Archive-663/lomoLCA/ASSETS/PHOTO/SAMPLE/fuji (3).jpg

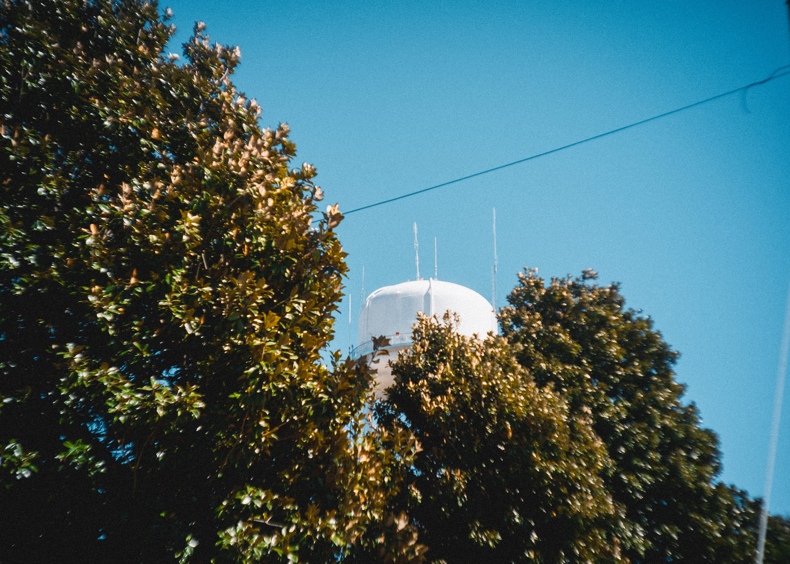
ASSETS/PHOTO/SAMPLE/fuji (3).jpg
