Archive-663/lomoLCA/ASSETS/PHOTO/SAMPLE/fuji (5).jpg

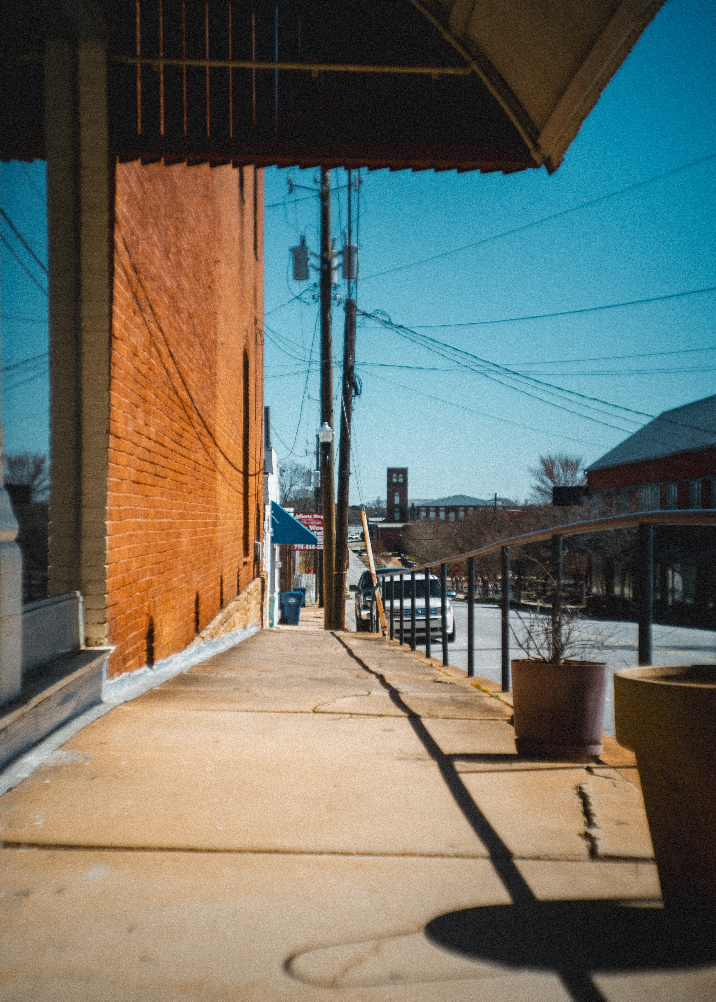
ASSETS/PHOTO/SAMPLE/fuji (5).jpg
