Archive-663/lomoLCA/ASSETS/PHOTO/SAMPLE/fuji (6).jpg

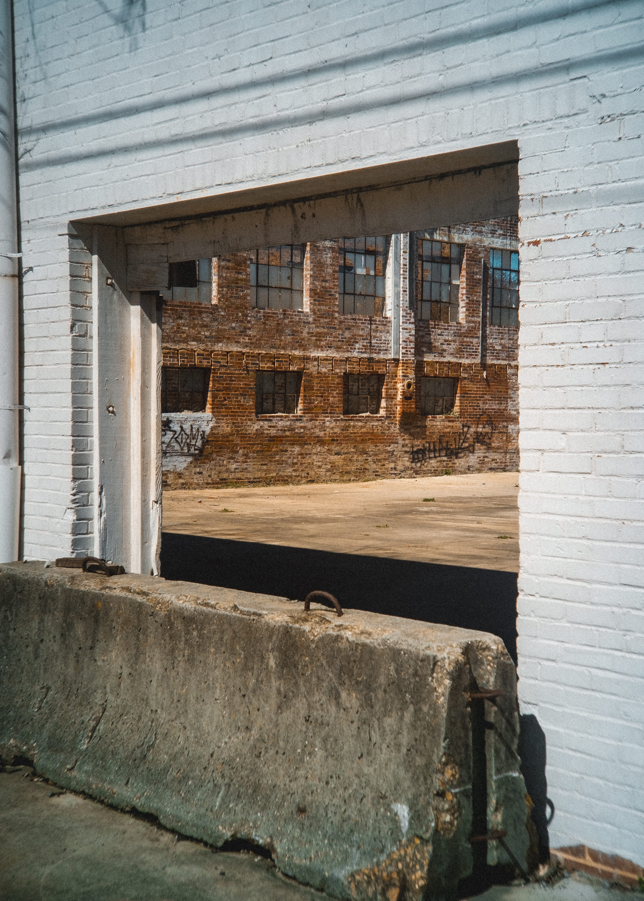
ASSETS/PHOTO/SAMPLE/fuji (6).jpg
