Archive-663/lomoLCA/ASSETS/PHOTO/SAMPLE/fuji (8).jpg

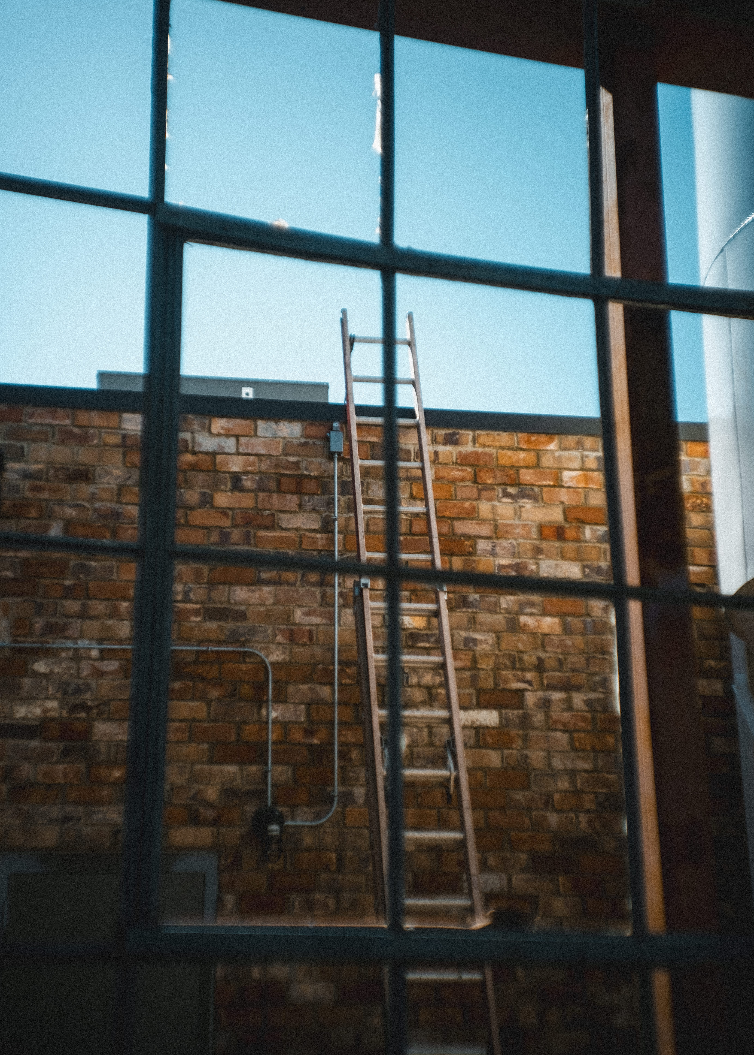
ASSETS/PHOTO/SAMPLE/fuji (8).jpg
