Archive-663/lomoLCA/ASSETS/PHOTO/SAMPLE/fuji (9).jpg

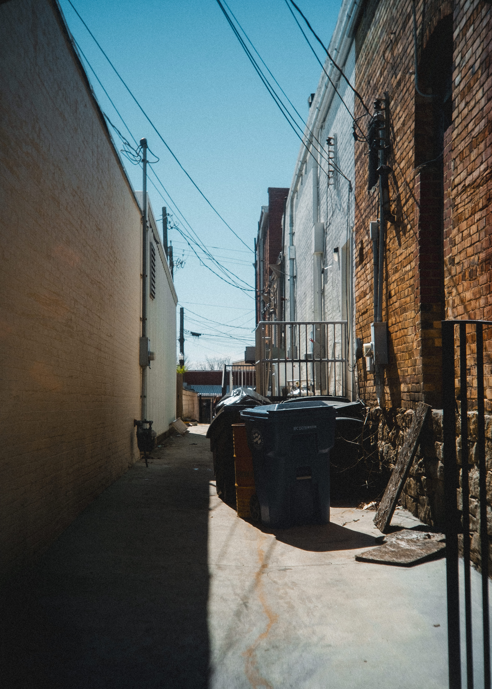
ASSETS/PHOTO/SAMPLE/fuji (9).jpg
