Archive-663/lomoLCA/ASSETS/PHOTO/SAMPLE/fuji (12).jpg

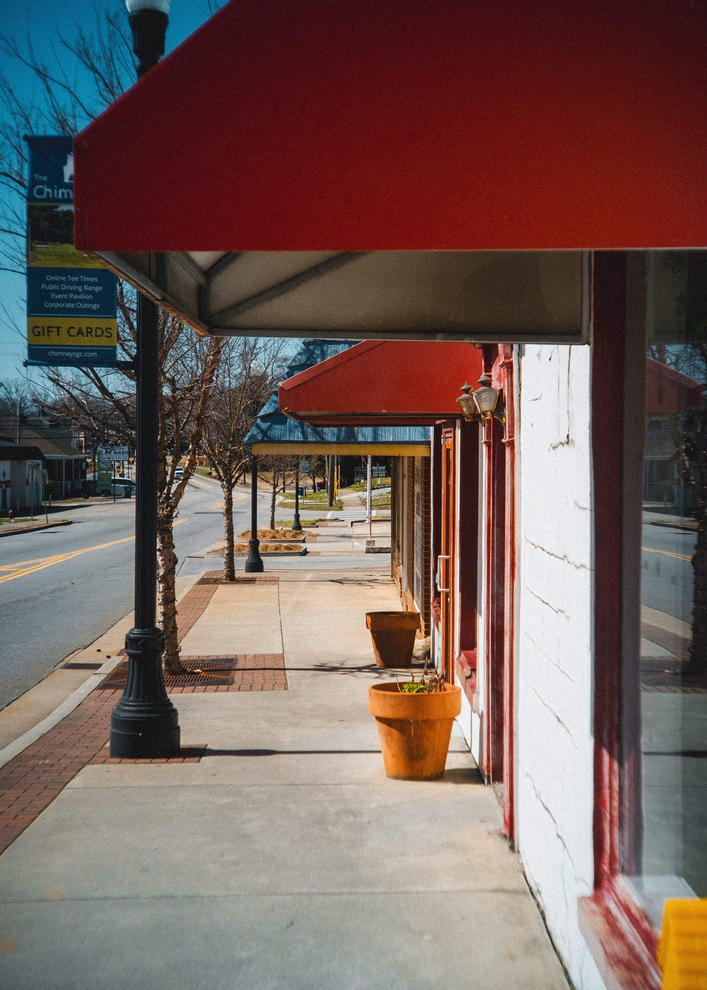
ASSETS/PHOTO/SAMPLE/fuji (12).jpg
