Archive-663/lomoLCA/ASSETS/PHOTO/SAMPLE/fuji (13).jpg

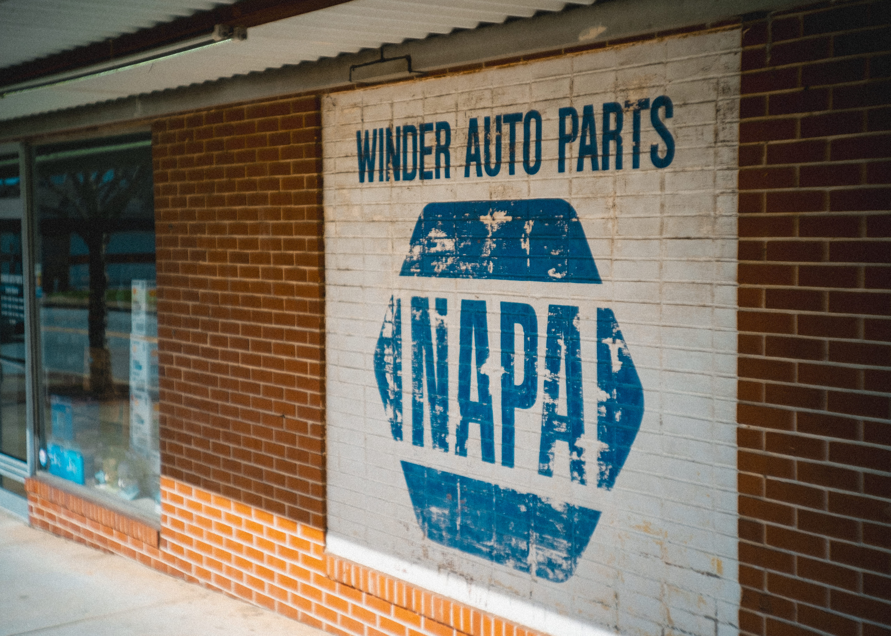
ASSETS/PHOTO/SAMPLE/fuji (13).jpg
