Archive-663/lomoLCA/Lomo LCA Main Rehousing/STEP/lomo_LCA_lensBase.stp

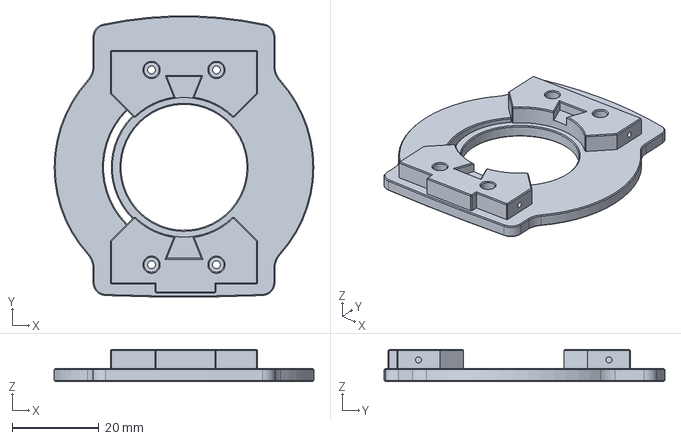
[picture p40: CAD file, 2024-03-15]
Lomo LCA Main Rehousing/STEP/lomo_LCA_lensBase.stp
60.0 x 64.9 x 7.40 mm
