Archive-663/lomoLCA/Lomo LCA Main Rehousing/STL/lomo_LCA_lensFacePlate_LOMO.stl

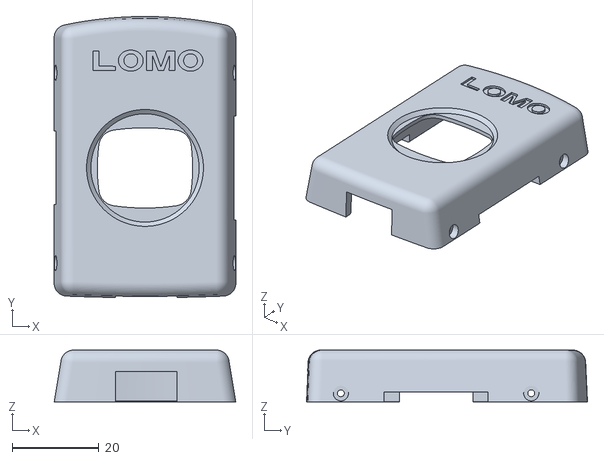
[picture p41: CAD file, 2024-03-15]
Lomo LCA Main Rehousing/STL/lomo_LCA_lensFacePlate_LOMO.stl
42.0 x 64.9 x 12.0
