Archive-663/lomoLCA/Nikon Z-mount/STEP/lomo_LCA_nikonZ_cap.stp

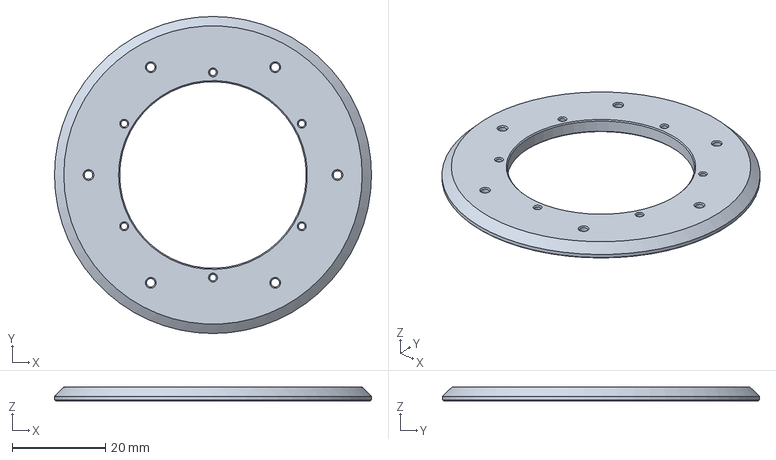
[picture p42: CAD file, 2024-03-15]
Nikon Z-mount/STEP/lomo_LCA_nikonZ_cap.stp
68.0 x 68.0 x 3.00 mm
