Archive-663/lomoLCA/Lomo LCA Main Rehousing/STEP/lomo_LCA_lensShutter_1.stp

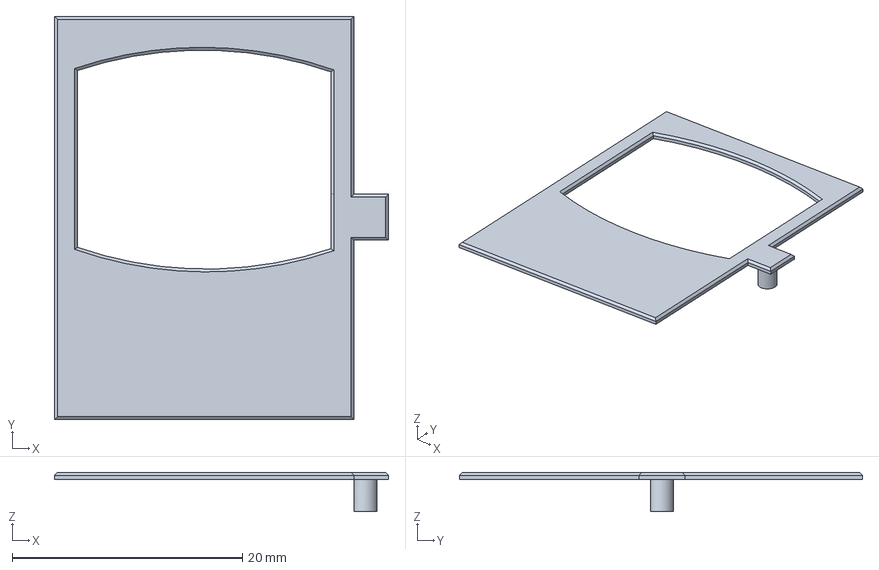
[picture p43: CAD file, 2024-03-15]
Lomo LCA Main Rehousing/STEP/lomo_LCA_lensShutter_1.stp
29.0 x 35.0 x 3.40 mm
