Archive-663/lomoLCA/Lomo LCA Main Rehousing/STEP/lomo_LCA_apertureBlade_1.stp

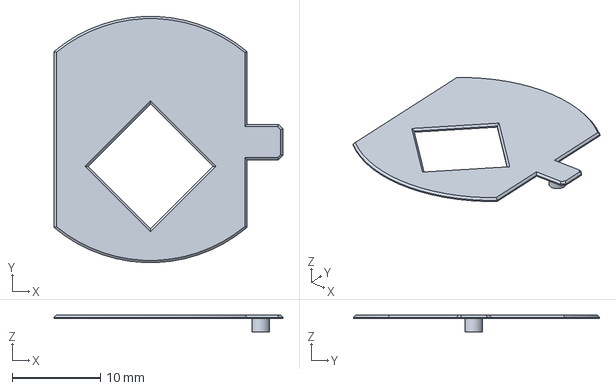
[picture p44: CAD file, 2024-03-15]
Lomo LCA Main Rehousing/STEP/lomo_LCA_apertureBlade_1.stp
25.9 x 27.9 x 1.90 mm
