Archive-663/lomoLCA/Lomo LCA Main Rehousing/STEP/lomo_LCA_shutterClutch.stp

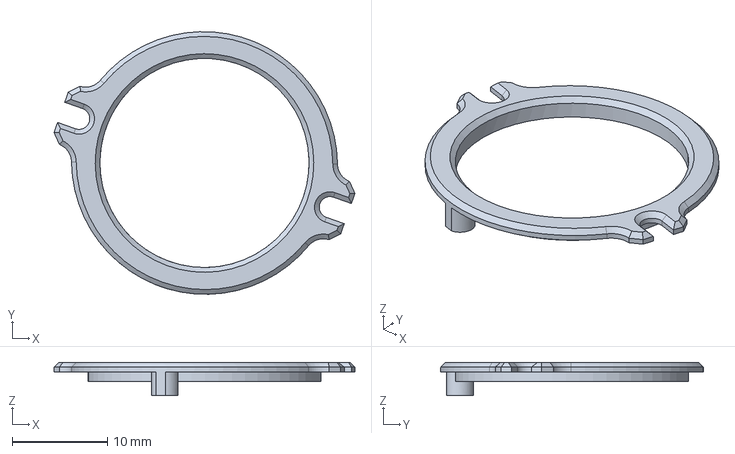
[picture p45: CAD file, 2024-03-15]
Lomo LCA Main Rehousing/STEP/lomo_LCA_shutterClutch.stp
31.7 x 27.6 x 3.50 mm
