Archive-663/lomoLCA/Lomo LCA Main Rehousing/STEP/lomo_LCA_apertureLever.stp

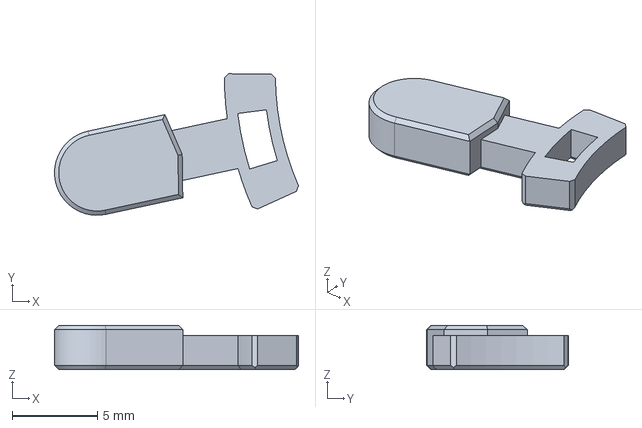
[picture p46: CAD file, 2024-03-15]
Lomo LCA Main Rehousing/STEP/lomo_LCA_apertureLever.stp
14.3 x 8.32 x 2.60 mm
