Archive-663/lomoLCA/Lomo LCA Main Rehousing/STEP/lomo_LCA_shutterClutchSlide.stp

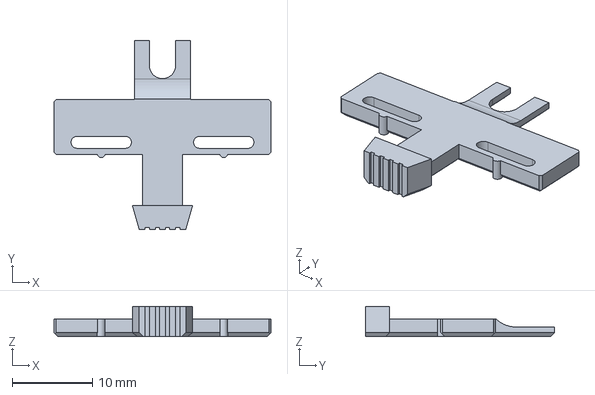
[picture p47: CAD file, 2024-03-15]
Lomo LCA Main Rehousing/STEP/lomo_LCA_shutterClutchSlide.stp
27.0 x 23.5 x 3.75 mm
