Archive-663/lomoLCA/Lomo LCA Main Rehousing/STEP/lomo_LCA_apertureClutch.stp

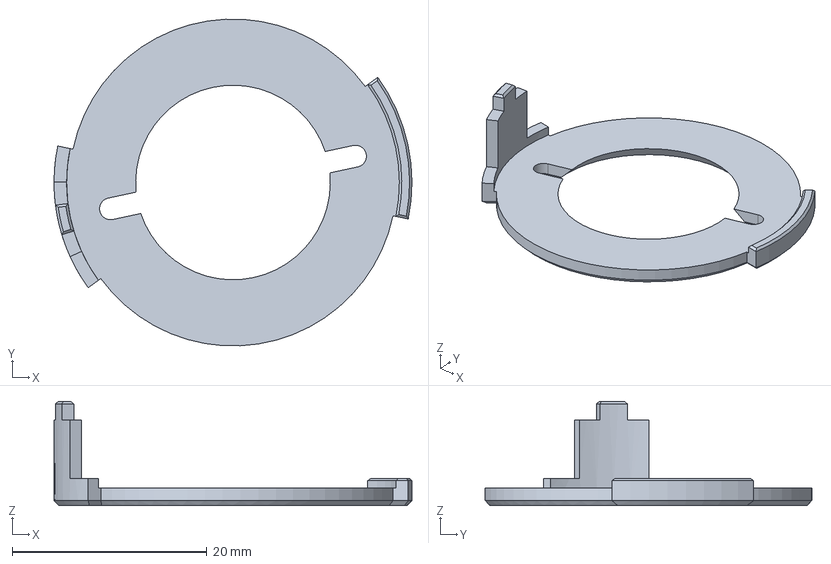
[picture p48: CAD file, 2024-03-15]
Lomo LCA Main Rehousing/STEP/lomo_LCA_apertureClutch.stp
36.8 x 33.6 x 10.7 mm
