Archive-663/lomoLCA/Lomo LCA Main Rehousing/STEP/lomo_LCA_shutterTrack_cap.stp

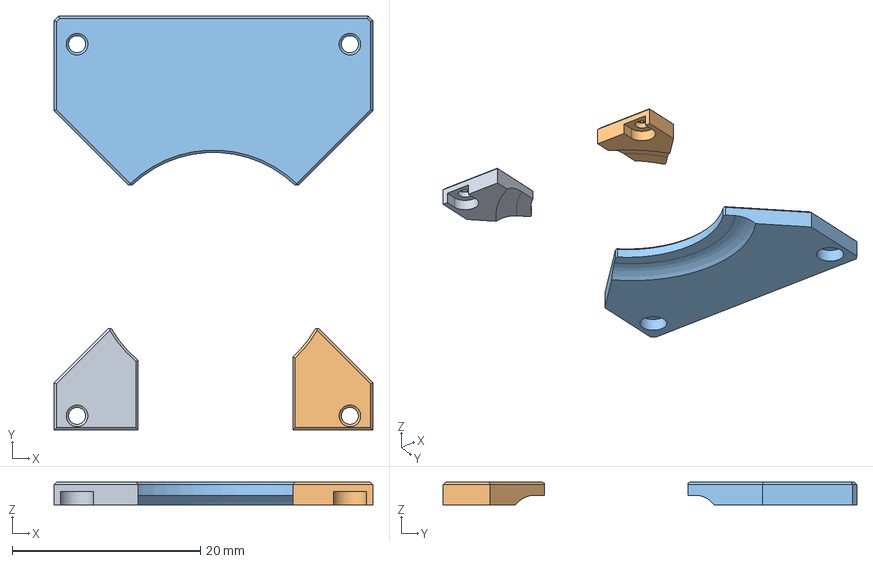
[picture p49: CAD file, 2024-03-15]
Lomo LCA Main Rehousing/STEP/lomo_LCA_shutterTrack_cap.stp
33.9 x 44.0 x 2.40 mm
