Archive-663/lomoLCA/Lomo LCA Main Rehousing/STEP/lomo_LCA_focusLock.stp

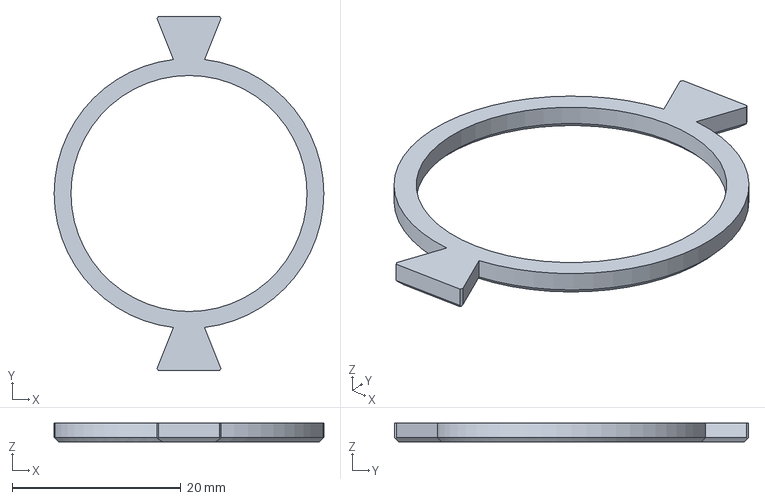
[picture p50: CAD file, 2024-03-15]
Lomo LCA Main Rehousing/STEP/lomo_LCA_focusLock.stp
32.0 x 42.0 x 2.20 mm
